KianLWP/Final-Year-Research-Project-2020/CAD/KiCAD Schematic/Schematic.kicad_pcb

## EAGLE design schema/mjBeep/boardBase2.sch

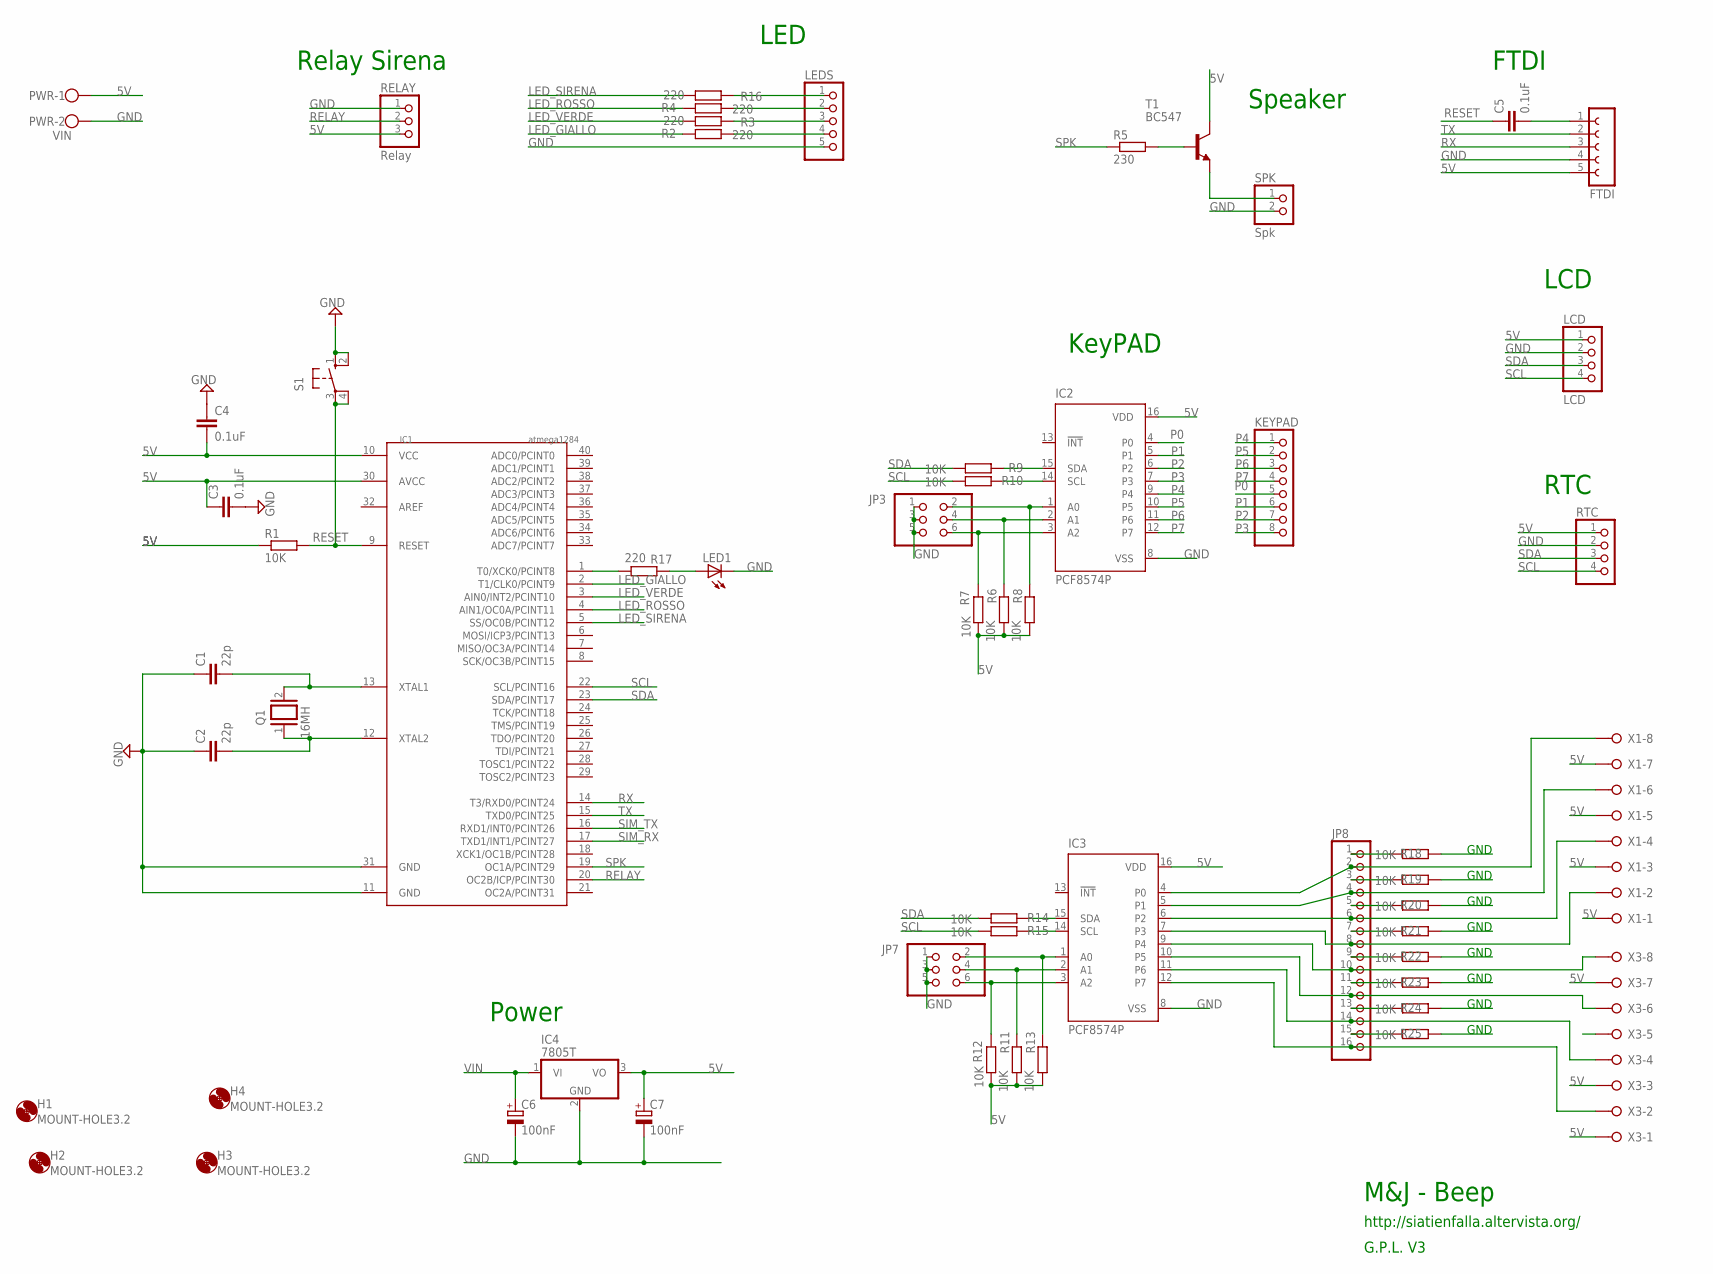
[picture p5: schematic boardBase2.sch]

Parts:
C1, C2: 22p; C025-024X044
C3, C4, C5: 0.1uF; C025-025X050
C6, C7: 100nF; E3,5-10
FTDI: FE05-1
H1, H2, H3, H4: MOUNT-HOLE3.2; 3,2
IC1: atmega1284; DIL40
IC2, IC3: PCF8574P; DIL16
IC4: 7805T; TO220H
JP3, JP7: PINHD-2X3; 2X03
JP8: PINHD-1X16; 1X16
KEYPAD: PINHD-1X8; 1X08
LCD: LCD; 1X04
LED1: LED3MM
LEDS: PINHD-1X5; 1X05
PWR: VIN; W237-102
Q1: 16MH; QS
R1, R6, R7, R8, R9, R10: 10K; 0207/10
R2, R3, R4, R16, R17: 220; 0207/2V
R5: 230; 0207/10
R11, R12, R13, R14, R15, R18, R19, R20, R21, R22, R23, R24, R25: 10K; 0207/2V
RELAY: Relay; 1X03
RTC: PINHD-1X4; 1X04
S1: 10-XX; B3F-10XX
SPK: Spk; 1X02
T1: BC547; TO92
X1, X3: W237-08P; W237-8P

Connections:
5V: C3.1, C4.2, C7.+, FTDI.5, IC1.10 (VCC), IC1.30 (AVCC), IC2.16 (VDD), IC3.16 (VDD), IC4.3 (VO), LCD.1, PWR.1, R1.1, R6.1, R7.2, R8.1, R11.1, R12.2, R13.1, RELAY.3, RTC.1, T1.3 (C), X1.1, X1.3, X1.5, X1.7, X3.1, X3.3, X3.5, X3.7
GND: C1.1, C2.1, C3.2, C4.1, C6.-, C7.-, FTDI.4, IC1.11 (GND), IC1.31 (GND), IC2.8 (VSS), IC3.8 (VSS), IC4.2 (GND), JP3.1, JP3.3, JP3.5, JP7.1, JP7.3, JP7.5, LCD.2, LED1.K (C), LEDS.5, PWR.2, R18.1, R19.1, R21.1, R22.1, R23.1, R24.1, R25.1, RELAY.1, RTC.2, S1.1 (S), S1.2 (S1), SPK.2
LED_GIALLO: IC1.2 (T1/CLK0/PCINT9), R2.2
LED_ROSSO: IC1.4 (AIN1/OC0A/PCINT11), R4.2
LED_SIRENA: IC1.5 (SS/OC0B/PCINT12), R16.1
LED_VERDE: IC1.3 (AIN0/INT2/PCINT10), R3.1
unnamed: C2.2, IC1.12 (XTAL2), Q1.1
unnamed: C1.2, IC1.13 (XTAL1), Q1.2
unnamed: IC2.1 (A0), JP3.2, R8.2
unnamed: C5.2, FTDI.1
unnamed: IC2.2 (A1), JP3.4, R6.2
unnamed: IC2.3 (A2), JP3.6, R7.1
unnamed: LEDS.4, R2.1
unnamed: LEDS.3, R3.2
unnamed: LEDS.2, R4.1
unnamed: IC2.14 (SCL), R10.1
unnamed: R5.2, T1.2 (B)
unnamed: SPK.1, T1.1 (E)
unnamed: IC2.15 (SDA), R9.1
unnamed: IC3.1 (A0), JP7.2, R13.2
unnamed: IC3.2 (A1), JP7.4, R11.2
unnamed: IC3.3 (A2), JP7.6, R12.1
unnamed: IC3.14 (SCL), R15.1
unnamed: IC3.15 (SDA), R14.1
unnamed: LEDS.1, R16.2
unnamed: IC1.1 (T0/XCK0/PCINT8), R17.1
unnamed: LED1.A, R17.2
unnamed: IC3.4 (P0), JP8.2, X1.8
unnamed: IC3.5 (P1), JP8.4, X1.6
unnamed: IC3.6 (P2), JP8.6, X1.4
unnamed: IC3.7 (P3), JP8.8, X1.2
unnamed: IC3.9 (P4), JP8.10, X3.8
unnamed: IC3.10 (P5), JP8.12, X3.6
unnamed: IC3.11 (P6), JP8.14, X3.4
unnamed: IC3.12 (P7), JP8.16, X3.2
unnamed: JP8.1, R18.2
unnamed: JP8.3, R19.2
unnamed: JP8.5, R20.2
unnamed: JP8.7, R21.2
unnamed: JP8.9, R22.2
unnamed: JP8.11, R23.2
unnamed: JP8.13, R24.2
unnamed: JP8.15, R25.2
P0: IC2.4 (P0), KEYPAD.5
P1: IC2.5 (P1), KEYPAD.6
P2: IC2.6 (P2), KEYPAD.7
P3: IC2.7 (P3), KEYPAD.8
P4: IC2.9 (P4), KEYPAD.1
P5: IC2.10 (P5), KEYPAD.2
P6: IC2.11 (P6), KEYPAD.3
P7: IC2.12 (P7), KEYPAD.4
RELAY: IC1.20 (OC2B/ICP/PCINT30), RELAY.2
RESET: C5.1, IC1.9 (RESET), R1.2, S1.3, S1.4 (P1)
RX: FTDI.3, IC1.14 (T3/RXD0/PCINT24)
SCL: IC1.22 (SCL/PCINT16), LCD.4, R10.2, R15.2, RTC.4
SDA: IC1.23 (SDA/PCINT17), LCD.3, R9.2, R14.2, RTC.3
SIM_RX: IC1.17 (TXD1/INT1/PCINT27)
SIM_TX: IC1.16 (RXD1/INT0/PCINT26)
SPK: IC1.19 (OC1A/PCINT29), R5.1
TX: FTDI.2, IC1.15 (TXD0/PCINT25)
VIN: C6.+, IC4.1 (VI)

Notes on the sheet:
Speaker
Relay Sirena
LED
M&J - Beep
http://siatienfalla.altervista.org/
G.P.L. V3
FTDI
KeyPAD
GND
RTC
LCD
Power
