KianLWP/Final-Year-Research-Project-2020/CAD/KiCAD Schematic/Schematic.kicad_pcb

## EAGLE design schema/mjBeep/schedaSensori.sch

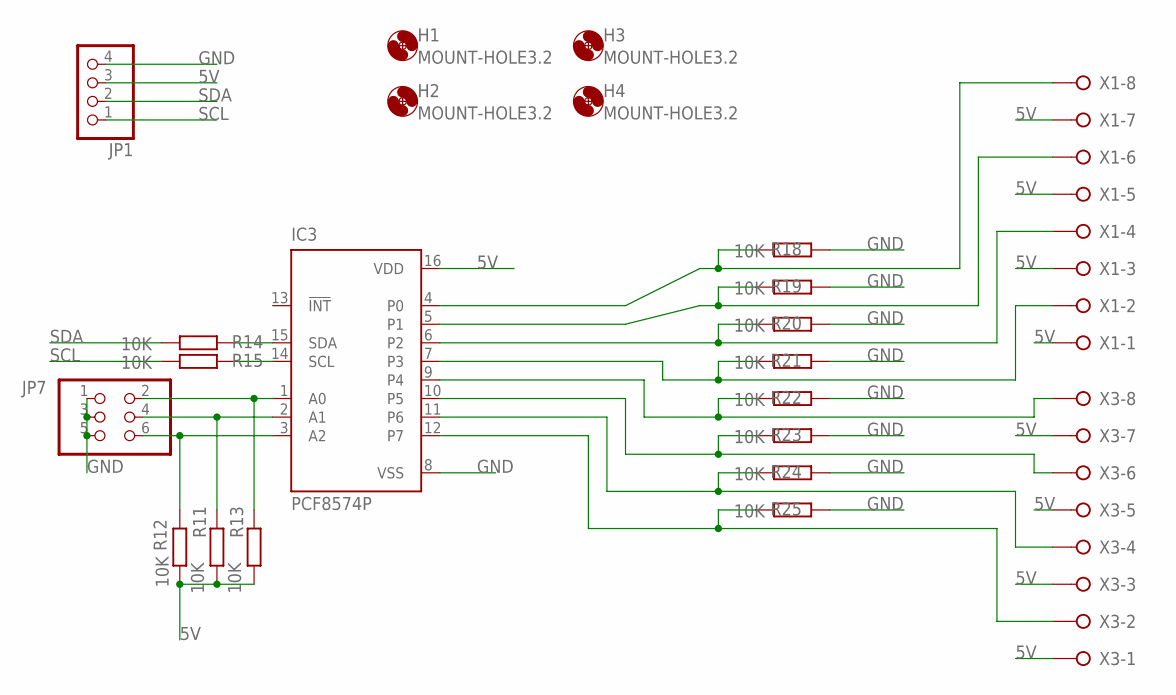
[picture p8: schematic schedaSensori.sch]

Parts:
H1, H2, H3, H4: MOUNT-HOLE3.2; 3,2
IC3: PCF8574P; DIL16
JP1: PINHD-1X4; 1X04
JP7: PINHD-2X3; 2X03
R11, R12, R13, R14, R15, R18, R19, R20, R21, R22, R23, R24, R25: 10K; 0207/10
X1, X3: W237-08P; W237-8P

Connections:
5V: IC3.16 (VDD), JP1.3, R11.1, R12.2, R13.1, X1.1, X1.3, X1.5, X1.7, X3.1, X3.3, X3.5, X3.7
GND: IC3.8 (VSS), JP1.4, JP7.1, JP7.3, JP7.5, R18.1, R19.1, R20.1, R21.1, R22.1, R23.1, R24.1, R25.1
unnamed: IC3.1 (A0), JP7.2, R13.2
unnamed: IC3.2 (A1), JP7.4, R11.2
unnamed: IC3.3 (A2), JP7.6, R12.1
unnamed: IC3.14 (SCL), R15.1
unnamed: IC3.15 (SDA), R14.1
unnamed: IC3.4 (P0), R18.2, X1.8
unnamed: IC3.5 (P1), R19.2, X1.6
unnamed: IC3.6 (P2), R20.2, X1.4
unnamed: IC3.7 (P3), R21.2, X1.2
unnamed: IC3.9 (P4), R22.2, X3.8
unnamed: IC3.10 (P5), R23.2, X3.6
unnamed: IC3.11 (P6), R24.2, X3.4
unnamed: IC3.12 (P7), R25.2, X3.2
SCL: JP1.1, R15.2
SDA: JP1.2, R14.2
